hugokernel/LeMurmureDuSon/cad/pattern/0.jpg

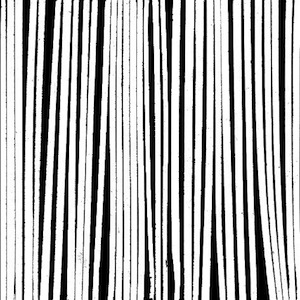
cad/pattern/0.jpg
