hugokernel/LeMurmureDuSon/cad/pattern/1.jpg

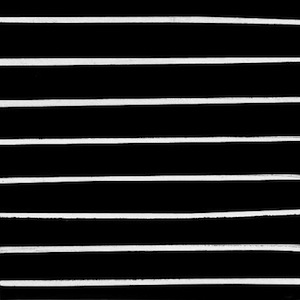
cad/pattern/1.jpg
