hugokernel/LeMurmureDuSon/cad/pattern/2.jpg

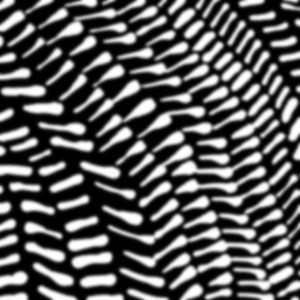
cad/pattern/2.jpg
