hugokernel/LeMurmureDuSon/cad/pattern/3.jpg

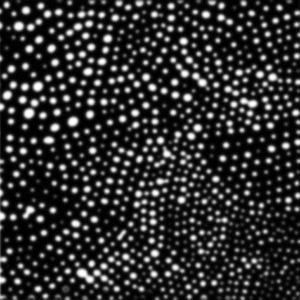
cad/pattern/3.jpg
