hugokernel/LeMurmureDuSon/cad/pattern/4.jpg

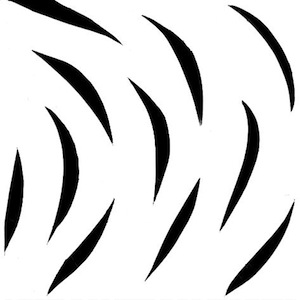
cad/pattern/4.jpg
