hugokernel/LeMurmureDuSon/cad/pattern/5.jpg

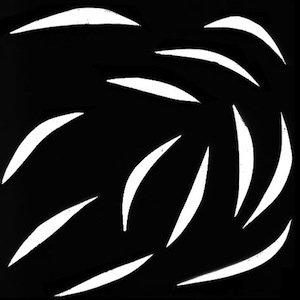
cad/pattern/5.jpg
